theacodes/genesynth/firmware/genesynth/thea.cpp

#include "thea.h"

namespace thea {

uint8_t tileset[61][8] = {
    {
        0b00000000, 0b00000000, 0b00000000, 0b00000000, 0b00000000, 0b00000000, 0b11000000, 0b11111000,
    },
    {
        0b00011110, 0b00011110, 0b11111110, 0b11111110, 0b11111110, 0b11111110, 0b00000000, 0b00000000,
    },
    {
        0b11111111, 0b11111111, 0b11111111, 0b00000000, 0b00000000, 0b11111110, 0b11111110, 0b11111110,
    },
    {
        0b11110000, 0b11111110, 0b11111111, 0b01111111, 0b00001111, 0b00000111, 0b11000111, 0b11100011,
    },
    {
        0b00000000, 0b00000000, 0b00000000, 0b00000000, 0b00000000, 0b00000000, 0b00000000, 0b00000000,
    },
    {
        0b00000011, 0b00000011, 0b00000011, 0b00000011, 0b00000011, 0b00000011, 0b00000011, 0b00000011,
    },
    {
        0b00011111, 0b11111111, 0b11111111, 0b11111100, 0b11100000, 0b00000000, 0b00000000, 0b00000000,
    },
    {
        0b11111110, 0b11111110, 0b11111110, 0b11111110, 0b00011110, 0b00011110, 0b00011110, 0b00011110,
    },
    {
        0b10001110, 0b10001110, 0b10001110, 0b10001110, 0b10001111, 0b10001111, 0b10001111, 0b10001111,
    },
    {
        0b00000000, 0b00000000, 0b11111111, 0b11111111, 0b11111111, 0b11111111, 0b00000000, 0b00000000,
    },
    {
        0b00000011, 0b00000001, 0b00000000, 0b00000000, 0b00000011, 0b00000011, 0b00000011, 0b00000011,
    },
    {
        0b00000000, 0b00000000, 0b00000000, 0b10000000, 0b11110000, 0b11111110, 0b11111111, 0b00111111,
    },
    {
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
        uint8_t letter_column = letter_tile * 8 + column;
        if (letter_column > num_pixels)
          continue;

        auto pixel = tile[column] >> row & 0x1;
        if (pixel) {
          display->drawPixel((x * 8) + column, (y * 8) + row + offset);
        }
      }
    }
  }
};
};
