theacodes/genesynth/firmware/genesynth/algorithm_gfx.h

#ifndef THEA_ALGORITHM_GFX_H
#define THEA_ALGORITHM_GFX_H

#include <U8g2lib.h>

namespace thea {
namespace algorithm_gfx {

void draw_alg_0(U8G2 &);
void draw_alg_1(U8G2 &);
void draw_alg_2(U8G2 &);
void draw_alg_3(U8G2 &);
void draw_alg_4(U8G2 &);
void draw_alg_5(U8G2 &);
void draw_alg_6(U8G2 &);
void draw_alg_7(U8G2 &);

} // namespace algorithm_gfx
} // namespace thea

#endif
